dohlemusic/The-Ray/simulations/simulation.asc

C1: cap; 100n
C2: cap; 220p
C3: cap; 47n
C4: cap; 100n
C5: cap; 47µ
C6: cap; 100n
C7: cap; 220p
C8: cap; 47µ
D1: zener; 1N750
J1: njf; J201
R1: res; 11.5k
R2: res; 1k
R3: res; 24k
R4: res; 100k
R5: res; 5e5
R6: res; 1m
R7: res; 10k
R8: res; 1k
R9: res; 10k
R10: res; 10k
R11: res; 500k
R12: res; 10k
U1: NE5532
V1: voltage; 9
V3: voltage; 9
V4: voltage; wavefile=clean.wav
Named nets: 0, out
.tran 0 5000m 0
;.ac lin 1000 5 25k
.wave "out.wav" 16 96k V(out)
